adam-mcguinness/brokenClock/arduino/led_arrays.h

#ifndef LED_ARRAYS
#define LED_ARRAYS 

const uint16_t ledMap[720] PROGMEM = {  145,  295,  305,  248,  697,  481,  107,  458,  479,  192,  112,  274,  367,  393,  489,  514,  276,  431,  450,  284,  9,  7,  425,  42,  267,  2,  245,  170,  4,  689,  289,  201,  599,  118,  488,  34,  291,  409,  581,  577,  194,  677,  204,  386,  430,  390,  440,  123,  542,  101,  378,  129,  374,  522,  521,  380,  658,  460,  246,  641,  40,  209,  179,  494,  546,  468,  142,  334,  195,  65,  77,  701,  363,  94,  26,  105,  438,  669,  321,  417,  556,  229,  428,  320,  328,  263,  215,  385,  612,  717,  184,  64,  451,  168,  459,  72,  687,  60,  203,  547,  379,  330,  503,  147,  691,  657,  549,  593,  66,  200,  470,  255,  345,  247,  634,  310,  79,  388,  447,  218,  212,  455,  463,  133,  454,  716,  497,  69,  579,  397,  86,  422,  114,  155,  59,  249,  597,  337,  61,  283,  259,  73,  602,  472,  435,  633,  372,  80,  416,  469,  406,  250,  364,  167,  96,  227,  650,  484,  662,  319,  35,  52,  426,  41,  558,  652,  111,  550,  124,  18,  560,  464,  287,  23,  707,  371,  589,  206,  413,  260,  329,  404,  708,  198,  186,  146,  21,  25,  277,  325,  692,  50,  39,  207,  43,  222,  456,  670,  668,  660,  150,  135,  202,  163,  223,  162,  445,  705,  293,  113,  526,  220,  322,  165,  452,  68,  98,  673,  465,  572,  639,  491,  221,  316,  109,  252,  183,  588,  424,  466,  711,  297,  655,  63,  609,  318,  187,  332,  512,  375,  499,  48,  571,  432,  90,  241,  139,  681,  510,  461,  15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

#endif
